magerbak/n2k_dashboard_esp32/n2k_config.h

#pragma once

//#define TESTING       // Enable canned data and other testing features. Not for production.

//#define USE_METRIC            // Define to use m (depth), celcius (temp)
//#define USE_METRIC_PRESSURE   // Define to use mbar (pressure) vs inHg
